looseleif/cardiac-wearable/cardiac~wearable~misc/bones.jpg

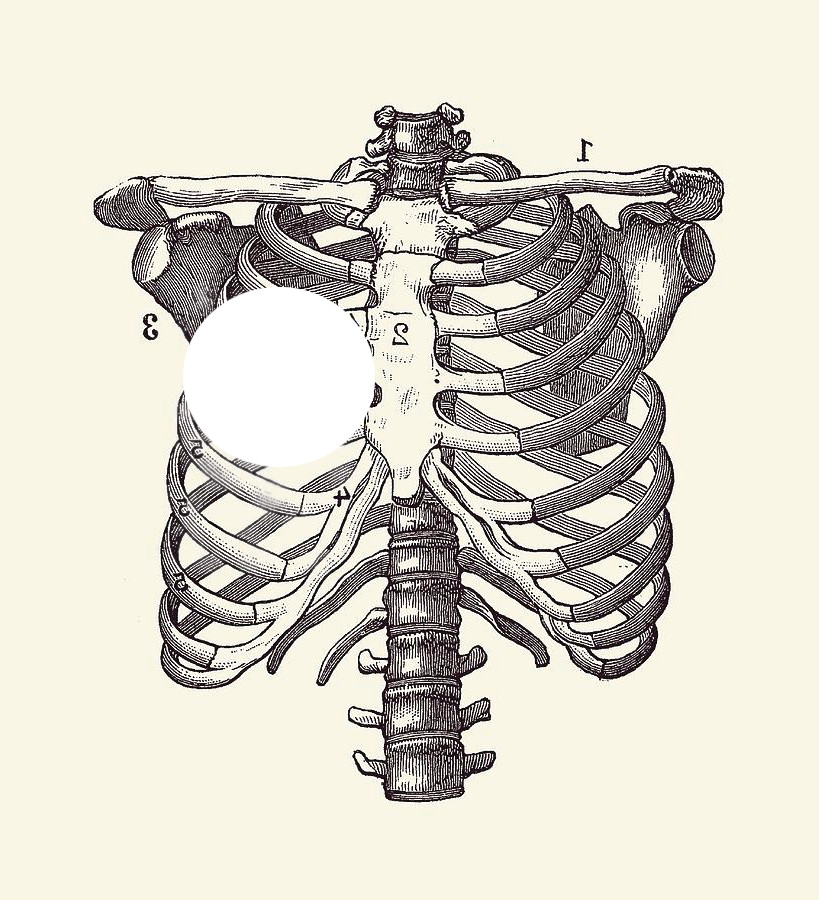
cardiac~wearable~misc/bones.jpg
