looseleif/cardiac-wearable/cardiac~wearable~misc/heart.png

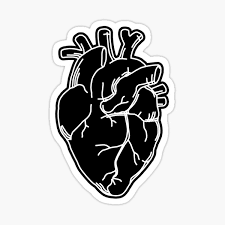
cardiac~wearable~misc/heart.png
