looseleif/cardiac-wearable/cardiac~wearable~misc/images/Final Presentation/Slide4.png

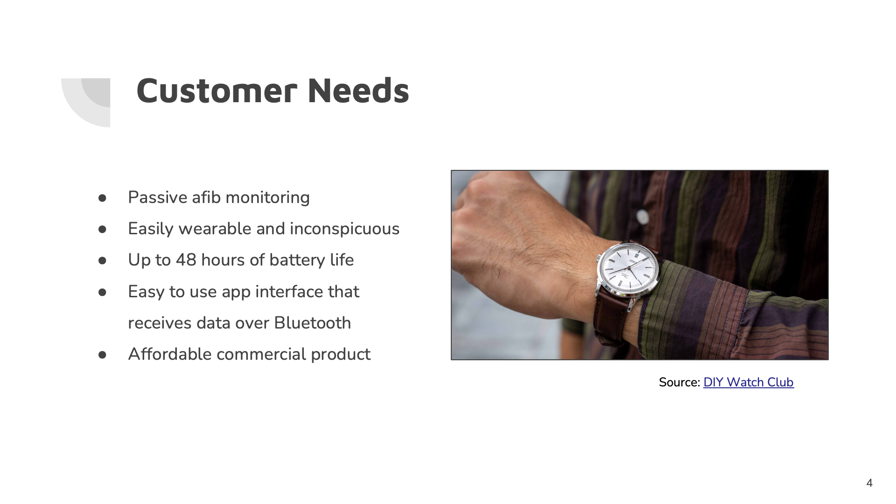
cardiac~wearable~misc/images/Final Presentation/Slide4.png
