looseleif/cardiac-wearable/cardiac~wearable~misc/images/Final Presentation/Slide14.png

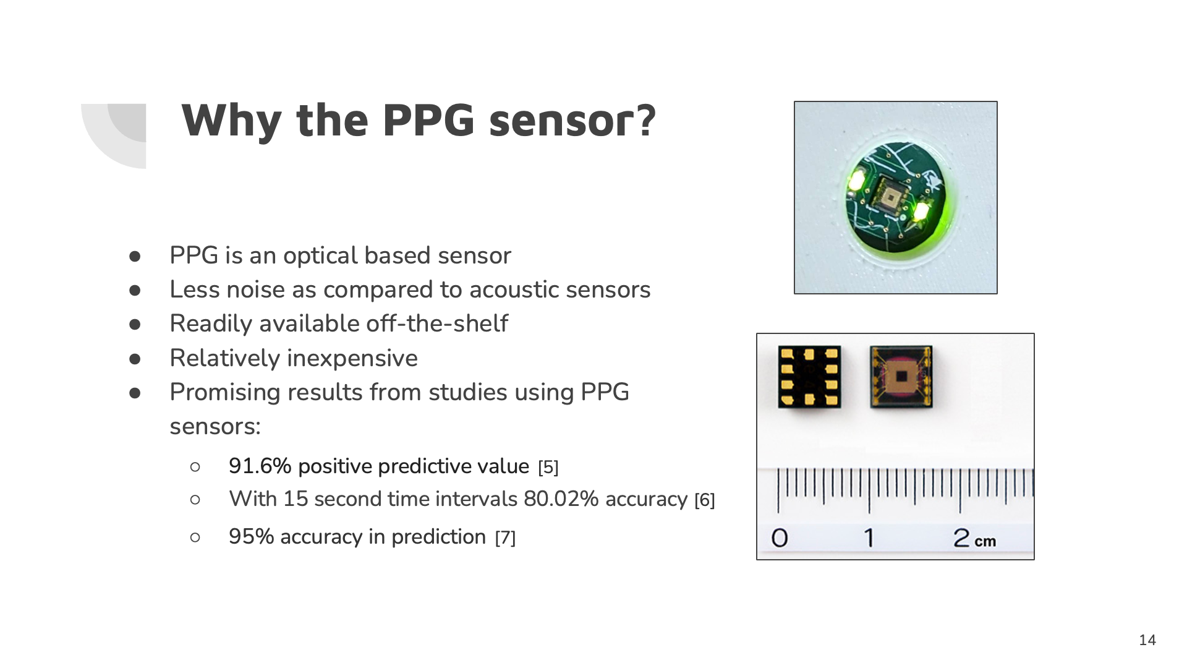
cardiac~wearable~misc/images/Final Presentation/Slide14.png
