looseleif/cardiac-wearable/cardiac~wearable~misc/images/Final Presentation/Slide19.png

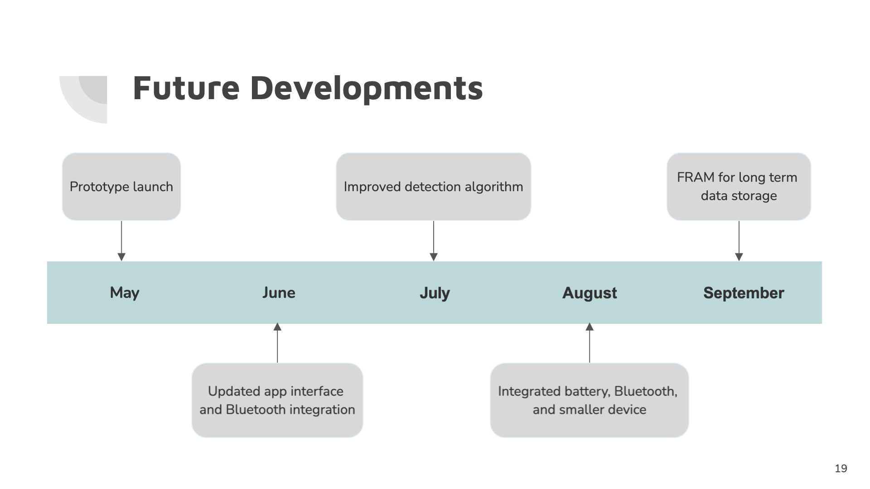
cardiac~wearable~misc/images/Final Presentation/Slide19.png
