looseleif/cardiac-wearable/cardiac~wearable~misc/images/Final Presentation/Slide20.png

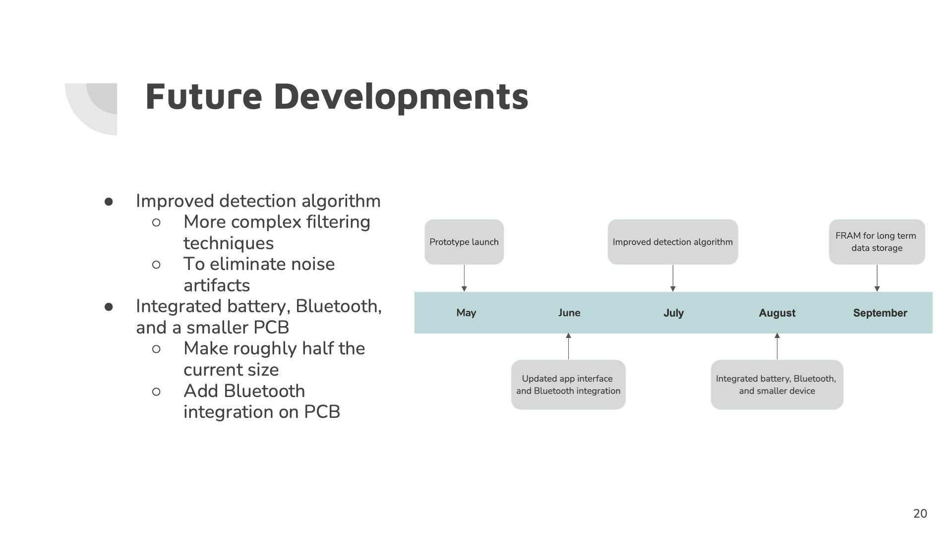
cardiac~wearable~misc/images/Final Presentation/Slide20.png
