looseleif/cardiac-wearable/cardiac~wearable~misc/images/Final Presentation/Slide21.png

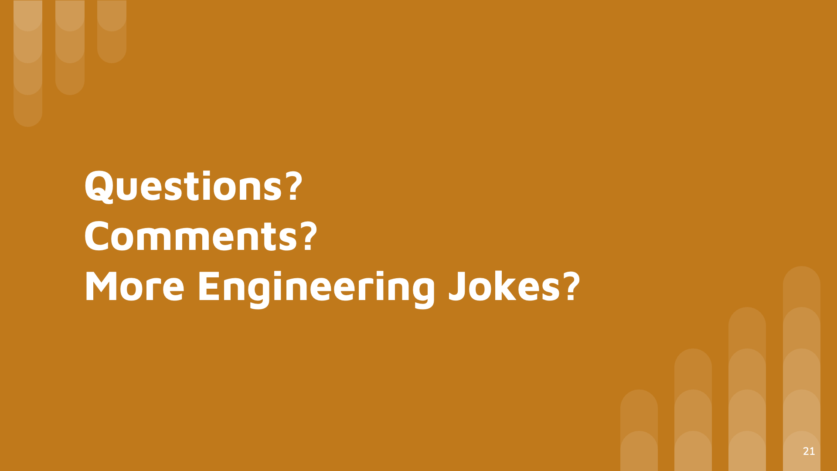
cardiac~wearable~misc/images/Final Presentation/Slide21.png
