looseleif/cardiac-wearable/cardiac~wearable~misc/images/nobg-awear-2.png

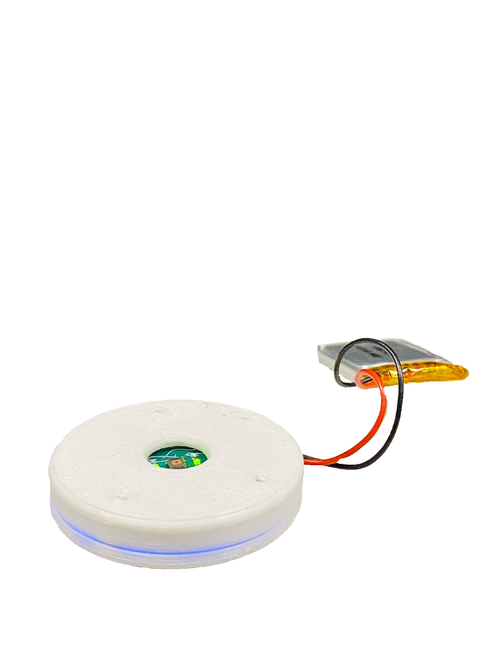
cardiac~wearable~misc/images/nobg-awear-2.png
