looseleif/cardiac-wearable/cardiac~wearable~misc/images/Screenshot 2023-06-20 at 11.44.25 PM.png

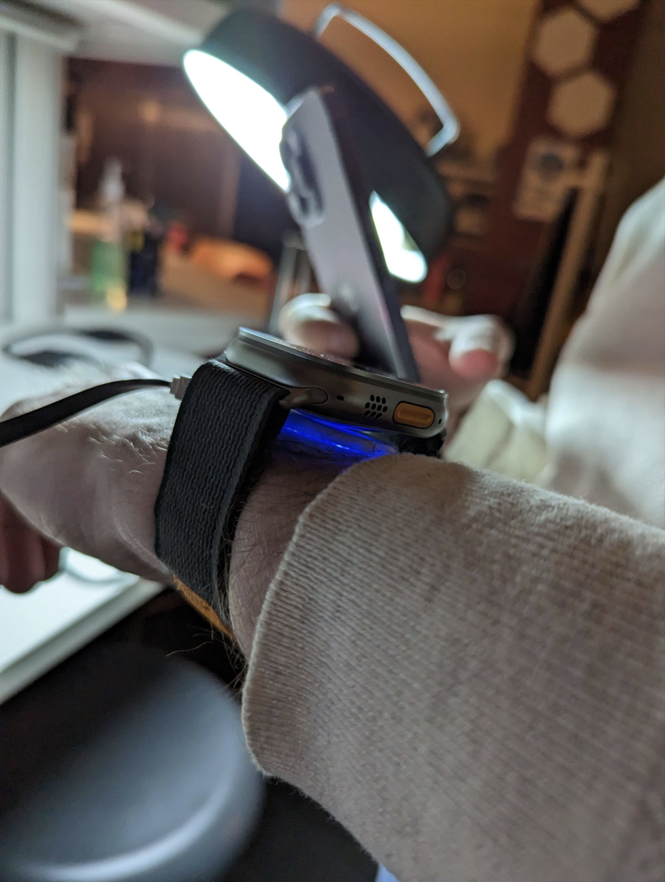
cardiac~wearable~misc/images/Screenshot 2023-06-20 at 11.44.25 PM.png
