looseleif/cardiac-wearable/cardiac~wearable~misc/pic1.png

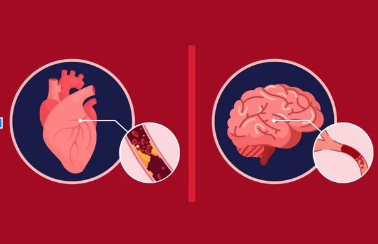
cardiac~wearable~misc/pic1.png
