looseleif/cardiac-wearable/cardiac~wearable~misc/static.png

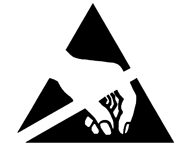
cardiac~wearable~misc/static.png
