looseleif/cardiac-wearable/cardiac~wearable~misc/veins.png

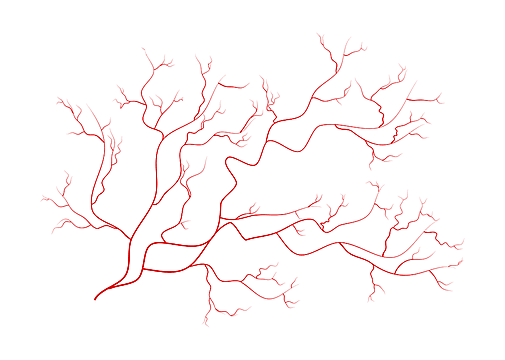
cardiac~wearable~misc/veins.png
