looseleif/cardiac-wearable/cardiac~wearable~misc/wearable.png

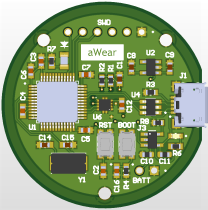
cardiac~wearable~misc/wearable.png
