looseleif/cardiac-wearable/cardiac~wearable~misc/wearableBack.png

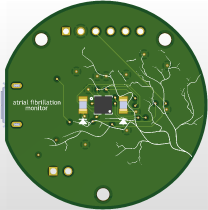
cardiac~wearable~misc/wearableBack.png
