looseleif/cardiac-wearable/cardiac-wearable-firmware/AWEAR_proj/Core/Src/BH1790GLC.c

/*****************************************************************************
  BH1790GLC.cpp

  Apr 13, 2023
  Vaibhav Shirole
******************************************************************************/
#include "BH1790GLC.h"


/*****************************************************************************
INIT FUNCTION
******************************************************************************/
uint8_t BH1790GLC_init( BH1790GLC *dev, I2C_HandleTypeDef *i2cHandle )
{
	/* Set struct parameters */
	dev->i2cHandle = i2cHandle;
	dev->ppg_data[0] = 0;
	dev->ppg_data[1] = 0;

	dev->samples_index = 0;

	for(int i=0; i<NUM_SAMPLES; i++){
		dev->smooth_array[i] = 0;
	}

	/* Keep count of errors */
	HAL_StatusTypeDef status;

	/* Take initial reads to make sure I2C is working */
	uint8_t regData;
	status = read(dev, BH1790GLC_MANUFACTURER_ID, &regData);	//get manufacturer id
	if(status != HAL_OK){
		return ERR_MID_VAL;
	}
	if(regData != BH1790GLC_MID_VAL){
		return ERR_MID_VAL;
	}

	status = read(dev, BH1790GLC_PART_ID, &regData);	//get part id
	if(status != HAL_OK){
		return ERR_PID_VAL;
	}
	if(regData != BH1790GLC_PID_VAL){
		return ERR_PID_VAL;
	}

	/* Configure the 3 registers needed to start taking measurements */
	uint8_t configData[3];
	configData[0] = BH1790GLC_MEAS_CONTROL1_VAL;	//to BH1790GLC_MEAS_CONTROL1 (0x41)
	configData[1] = BH1790GLC_MEAS_CONTROL2_VAL;	//to BH1790GLC_MEAS_CONTROL2 (0x42)
	configData[2] = BH1790GLC_MEAS_START_VAL;		//to BH1790GLC_MEAS_START (0x43)

	status = write(dev, BH1790GLC_MEAS_CONTROL1, &configData[0]);
	if(status != HAL_OK){
		return ERR_MEAS_CONTROL1;
	}
	status = write(dev, BH1790GLC_MEAS_CONTROL2, &configData[1]);
	if(status != HAL_OK){
		return ERR_MEAS_CONTROL2;
	}
	status = write(dev, BH1790GLC_MEAS_START, &configData[2]);
	if(status != HAL_OK){
		return ERR_MEAS_START;
	}

	return SUCCESS;
}


/*****************************************************************************
DATA ACQUISITION FUNCTIONS
******************************************************************************/
/*
 * Puts the ppg readings into the ppg_data struct variable
 */
uint8_t get_val( BH1790GLC *dev )
{
	HAL_StatusTypeDef status;
	uint8_t sensorData[4];

	status = many_reads(dev, BH1790GLC_DATAOUT_LEDOFF, sensorData, 4);
	if(status != HAL_OK){
		return ERR_DATA_OUT;		//error check
	}

	//convert the sensorData values to useful data
	dev->ppg_data[0] = ((uint16_t)sensorData[1]<<8)|(sensorData[0]);	//LED OFF
	dev->ppg_data[1] = ((uint16_t)sensorData[3]<<8)|(sensorData[2]);	//LED ON

	return SUCCESS;
}

/*
 * Writes “SWRESET=1” (Address 40h), when stop measurement or change parameter.
 * This will wipe all registers
 */
uint8_t reset_device( BH1790GLC *dev ){
	HAL_StatusTypeDef status;
	uint8_t configData = BH1790GLC_SWRESET;

	status = write(dev, BH1790GLC_RESET, &configData);
	if(status != HAL_OK){
		return ERR_RESET;
	}

	return SUCCESS;
}

/*
 * Run this periodically (according to data sheet) after reading data
 */
uint8_t param_refreshment( BH1790GLC *dev ){
	/* Keep count of errors */
	HAL_StatusTypeDef status;

	/* Configure the 3 registers needed to start taking measurements */
	uint8_t configData[3];
	configData[0] = BH1790GLC_MEAS_CONTROL1_VAL;	//to BH1790GLC_MEAS_CONTROL1 (0x41)
	configData[1] = BH1790GLC_MEAS_CONTROL2_VAL;	//to BH1790GLC_MEAS_CONTROL2 (0x42)
	configData[2] = BH1790GLC_MEAS_START_VAL;		//to BH1790GLC_MEAS_START (0x43)

	status = write(dev, BH1790GLC_MEAS_CONTROL1, &configData[0]);
	if(status != HAL_OK){
		return ERR_MEAS_CONTROL1;
	}

	status = write(dev, BH1790GLC_MEAS_CONTROL2, &configData[1]);
	if(status != HAL_OK){
		return ERR_MEAS_CONTROL2;
	}

	status = write(dev, BH1790GLC_MEAS_START, &configData[2]);
	if(status != HAL_OK){
		return ERR_MEAS_START;
	}

	return SUCCESS;
}

uint8_t add_sample( BH1790GLC *dev ){


	dev->ppg_samples[dev->samples_index] = dev->ppg_data[1];
	dev->samples_index++;


	if(dev->samples_index==NUM_SAMPLES){

		dev->samples_index = 0;
		return 1;
	}
	else if(dev->ppg_data[0] > led_off_threshold) {
		dev->samples_index = 0;
	}

	return 0;
}

uint8_t ppg_calculate( BH1790GLC *dev ){


	  //uint16_t smooth_array[NUM_SAMPLES];
	  int deriv_array[NUM_SAMPLES-1];

	  uint16_t raw_data_1;
	  float smooth_data_1 = 0;
	  float lpf_beta = 0.075;

	  for(int i = 0; i < NUM_SAMPLES; i++){

		  raw_data_1 = dev->ppg_samples[i];
		  smooth_data_1 = smooth_data_1 - (lpf_beta*(smooth_data_1 - raw_data_1));
		  dev->smooth_array[i] = smooth_data_1;


		  if(i!=0){


			  int deriv = (int)dev->smooth_array[i] - (int)dev->smooth_array[i-1];
			  if(deriv<255 || deriv>-255){ // check 255 value later

				 deriv_array[i] = deriv;

			  } else {

				 deriv_array[i] = deriv_array[i-1];

			  }

		  }

	  }

	  int pos = 0;
	  int neg = 0;

	  int pos_check = 0;
	  int neg_check = 0;

	  int peak_vals[40] = {};
	  int peak_count = 0;


	  for(int j = 0; j < NUM_SAMPLES-1; j++){



		  if(deriv_array[j]>0 && pos_check==0){

			  neg = 0;
			  pos++;

			  if(pos==3){

				  pos_check = 1;

			  }

		  } else if (deriv_array[j]<0 && pos_check==1) {

			  pos = 0;
			  neg++;

			  if(neg==3){

				  neg_check = 1;
				  peak_vals[peak_count] = j;
				  peak_count++;

				  pos_check = 0;
				  neg_check = 0;

			  }


		  } else if (deriv_array[j]<0 && pos_check==0){
			  pos = 0;
		  }

	  }

	  //printf("{");

	  for(int k = 0; k<40; k++){

		  //printf("[%d],", peak_vals[k]);

	  }
	  //printf("}\n");

	  double sum = 0;

	  for (int k = 1; k < peak_count; k++) {
	    sum += peak_vals[k] - peak_vals[k - 1];
	  }

	  double mean_interval = sum / (peak_count - 1);

	  double squared_diff_sum = 0;
	  for (int k = 1; k < peak_count; k++) {
	    double diff = peak_vals[k] - peak_vals[k - 1] - mean_interval;
	    squared_diff_sum += diff * diff;
	  }

	  double std_deviation = sqrt(squared_diff_sum / (peak_count - 1));  // Calculate the standard deviation of the intervals
	  double cv = std_deviation / mean_interval; // Calculate the coefficient of variation (CV)

	  double cv_threshold;
	     int af_detected_cv = 0;
	     int af_detected_tpr = 0;

	     // Check for atrial fibrillation using cv threshold
	     if (peak_count >= 3 && peak_count <= 40)
	     {
	         cv_threshold = 0.624;// - (0.312 * (peak_count - 3)) / (40 - 3);

	         if (cv > cv_threshold)
	         {
	             af_detected_cv = 1;
	         }
	     }

	     // Calculate turning point ratio
	     int turning_points = 0;

	     for (int j = 1; j < NUM_SAMPLES-2; j++)
	     {
	         if ((deriv_array[j] > deriv_array[j - 1] && deriv_array[j] > deriv_array[j + 1]) ||
	             (deriv_array[j] < deriv_array[j - 1] && deriv_array[j] < deriv_array[j + 1]))
	         {
	             turning_points++;
	         }
	     }

	     double turning_point_ratio = (double)turning_points / (double)(NUM_SAMPLES-2);

	    // printf("Turning Point Ratio: %f\n", turning_point_ratio);

	     // Check for atrial fibrillation using turning point ratio threshold
	     double tpr_threshold = 0.375;
	     if (turning_point_ratio >= tpr_threshold)
	     {
	         af_detected_tpr = 1;
	     }

	     // Check if both CV and Turning Point Ratio conditions are met
	     if (af_detected_cv && af_detected_tpr)
	     {
	         printf("Atrial fibrillation detected.\n");
	     }
	     else
	     {
	         printf("Atrial fibrillation not detected.\n");
	     }

	     printf("Coefficient of Variation: %f\n", cv);
	     printf("Turning Point Ratio: %f\n", turning_point_ratio);


	 }




/*****************************************************************************
LOW-LEVEL FUNCTIONS
******************************************************************************/
/*
 * Writes a single byte to a specific register address
 * dev : device
 * reg : register to write to
 * data : what to write
 */
HAL_StatusTypeDef write( BH1790GLC *dev, uint8_t reg, uint8_t *data)
{
	HAL_StatusTypeDef ret;

	//passing my handle, read from peripheral, get from this register, size of that register,
	// where to put the data, 1 byte of data, max delay
	ret = HAL_I2C_Mem_Write(dev->i2cHandle, (BH1790GLC_DEVICE_ADDRESS<<1), reg, 1, data, 1, HAL_MAX_DELAY);
	if(ret != HAL_OK){
		return ret;			//error check
	}

	return HAL_OK;
}

/*
 * Reads a single byte from a specific register address
 * dev : device
 * reg : register to read from
 * data : stores what was read
 */
HAL_StatusTypeDef read( BH1790GLC *dev, uint8_t reg, uint8_t *data)
{
	HAL_StatusTypeDef ret;

	ret = HAL_I2C_Mem_Read(dev->i2cHandle, (BH1790GLC_DEVICE_ADDRESS<<1), reg, 1, data, 1, HAL_MAX_DELAY);
	if(ret != HAL_OK){
		return ret;			//error check
	}


	return HAL_OK;
}

/*
 * Reads n bytes from a starting register address
 * dev : device
 * reg : register to read from
 * data : stores what was read
 * length : number of registers to read (in bytes)
 */
HAL_StatusTypeDef many_reads( BH1790GLC *dev, uint8_t reg, uint8_t *data, uint8_t length )
{
	HAL_StatusTypeDef ret;

	ret = HAL_I2C_Mem_Read(dev->i2cHandle, (BH1790GLC_DEVICE_ADDRESS<<1), reg, 1, data, length, HAL_MAX_DELAY);
	if(ret != HAL_OK){
		return ret;			//error check
	}

	return HAL_OK;
}

//uint16_t raw_data[160] = {
//
//		  21893,
//		  21887,
//		  21887,
//		  21882,
//		  21904,
//		  21929,
//		  21926,
//		  21948,
//		  21965,
//		  21982,
//		  21998,
//		  21998,
//		  21995,
//		  22020,
//		  22023,
//		  22032,
//		  22023,
//		  22035,
//		  22045,
//		  22041,
//		  22026,
//		  21952,
//		  21857,
//		  21817,
//		  21818,
//		  21834,
//		  21832,
//		  21838,
//		  21856,
//		  21842,
//		  21831,
//		  21825,
//		  21828,
//		  21834,
//		  21848,
//		  21867,
//		  21896,
//		  21897,
//		  21902,
//		  21896,
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
//};
