looseleif/cardiac-wearable/cardiac-wearable-firmware/seeeduino/cardiac-wearable-firmware/src/BH1790GLC.cpp

/*****************************************************************************
  BH1790GLC.cpp

 Copyright (c) 2016 ROHM Co.,Ltd.

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
 THE SOFTWARE IS PROVIDED "AS IS", WITHOUT WARRANTY OF ANY KIND, EXPRESS OR
 IMPLIED, INCLUDING BUT NOT LIMITED TO THE WARRANTIES OF MERCHANTABILITY,
 FITNESS FOR A PARTICULAR PURPOSE AND NONINFRINGEMENT. IN NO EVENT SHALL THE
 AUTHORS OR COPYRIGHT HOLDERS BE LIABLE FOR ANY CLAIM, DAMAGES OR OTHER
 LIABILITY, WHETHER IN AN ACTION OF CONTRACT, TORT OR OTHERWISE, ARISING FROM,
 OUT OF OR IN CONNECTION WITH THE SOFTWARE OR THE USE OR OTHER DEALINGS IN
 THE SOFTWARE.
******************************************************************************/
//#include <avr/pgmspace.h>
#include <Arduino.h>
#include <Wire.h>
#include "BH1790GLC.h"

BH1790GLC::BH1790GLC(void)
{

}

byte BH1790GLC::init(void)
{
  byte rc;
  unsigned char reg;
  unsigned char val[3];

  rc = read(BH1790GLC_PART_ID, &reg, sizeof(reg));
  if (rc != 0) {
    //Serial.println(F("Can't access BH1790GLC"));
    return (rc);
  }
  //Serial.print(F("BH1790GLC Part ID Value = 0x"));
  //Serial.println(reg, HEX);

  if (reg != BH1790GLC_PID_VAL) {
    //Serial.println(F("Can't find BH1790GLC"));
    return (rc);
  }

  rc = read(BH1790GLC_MANUFACTURER_ID, &reg, sizeof(reg));
  if (rc != 0) {
    //Serial.println(F("Can't access BH1790GLC"));
    return (rc);
  }
  //Serial.print(F("BH1790GLC MANUFACTURER ID Register Value = 0x"));
  //Serial.println(reg, HEX);

  if (reg != BH1790GLC_MID_VAL) {
    //Serial.println(F("Can't find BH1790GLC"));
    return (rc);
  }

  val[0] = BH1790GLC_MEAS_CONTROL1_VAL;
  val[1] = BH1790GLC_MEAS_CONTROL2_VAL;
  val[2] = BH1790GLC_MEAS_START_VAL;  
  rc = write(BH1790GLC_MEAS_CONTROL1, val, sizeof(val));
  if (rc != 0) {
    //Serial.println("Can't write BH1790GLC MEAS_CONTROL1-MEAS_START register");
  }
  
  return (rc);
}

byte BH1790GLC::get_rawval(unsigned char *data)
{
  byte rc;

  rc = read(BH1790GLC_DATAOUT_LEDOFF, data, 4);
  if (rc != 0) {
    //Serial.println(F("Can't get BH1790GLC value"));
  }

  return (rc);
}

byte BH1790GLC::get_val(unsigned short *data)
{
  byte rc;
  unsigned char val[4];

  rc = get_rawval(val);
  if (rc != 0) {
    return (rc);
  }

  data[0] = ((unsigned short)val[1] << 8) | (val[0]);
  data[1] = ((unsigned short)val[3] << 8) | (val[2]);

  return (rc);  
}

byte BH1790GLC::write(unsigned char memory_address, unsigned char *data, unsigned char size)
{
  byte rc;

  Wire.beginTransmission(BH1790GLC_DEVICE_ADDRESS);
  Wire.write(memory_address);
  Wire.write(data, size);
  rc = Wire.endTransmission(true);
  return (rc);
}

byte BH1790GLC::read(unsigned char memory_address, unsigned char *data, int size)
{
  byte rc;
  unsigned char cnt;

  Wire.beginTransmission(BH1790GLC_DEVICE_ADDRESS);
  Wire.write(memory_address);
  rc = Wire.endTransmission(false);
  if (rc != 0) {
    return (rc);
  }

  Wire.requestFrom(BH1790GLC_DEVICE_ADDRESS, size, true);
  cnt = 0;
  while(Wire.available()) {
    data[cnt] = Wire.read();
    cnt++;
  }

  return (0);
}
